doducminh/3d-models-hydroponic-bonsai-root-cradle/gcode/funnel-L.png

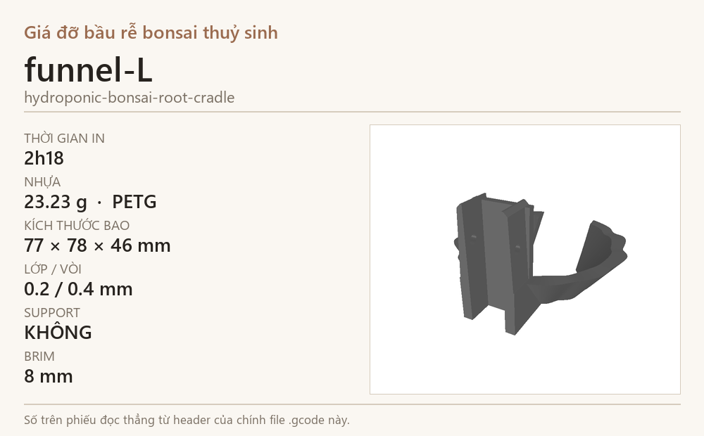
gcode/funnel-L.png
