doducminh/3d-models-hydroponic-bonsai-root-cradle/gcode/gate-L.png

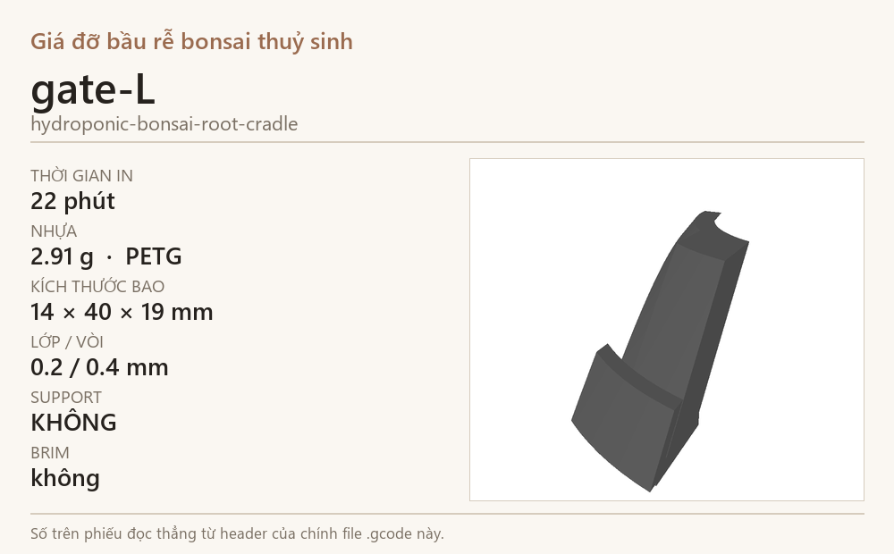
gcode/gate-L.png
